ptrckfrnk/sleep-position-classification/Sleep_position_classifier_PSoC.cydsn/I2C_Interface.h

/* ===============================================
 *
 * Alfonzo Massimo, Canavate Chloé, Franke Patrick
 * Project 05 - Sleep Position Classifier
 * Electronic Technologies and Biosensor Laboratory
 * Academic year 2021 - 2022
 * I2C_Interface.h file
 * \brief Hardware specific I2C interface
 *
 * =============================================== */


#ifndef __I2C_Interface_H
    #define __I2C_Interface_H
    
    #include "cytypes.h"
    #include "ErrorCodes.h"
    
    /** \brief Start the I2C peripheral.
    *   
    *   This function starts the I2C peripheral so that it is ready to work.
    */
    ErrorCode I2C_Peripheral_Start(void);
    
    /** \brief Stop the I2C peripheral.
    *   
    *   This function stops the I2C peripheral from working.
    */
    ErrorCode I2C_Peripheral_Stop(void);
    
    /**
    *   \brief Read one byte over I2C.
    *   
    *   This function performs a complete reading operation over I2C from a single
    *   register.
    *   \param device_address I2C address of the device to talk to.
    *   \param register_address Address of the register to be read.
    *   \param data Pointer to a variable where the byte will be saved.
    */
    ErrorCode I2C_Peripheral_ReadRegister(uint8_t device_address, 
                                          uint8_t register_address,
                                          uint8_t* data);
    
    /** 
    *   \brief Read multiple bytes over I2C.
    *   
    *   This function performs a complete reading operation over I2C from multiple
    *   registers.
    *   \param device_address I2C address of the device to talk to.
    *   \param register_address Address of the first register to be read.
    *   \param register_count Number of registers we want to read.
    *   \param data Pointer to an array where data will be saved.
    */
    ErrorCode I2C_Peripheral_ReadRegisterMulti(uint8_t device_address,
                                               uint8_t register_address,
                                               uint8_t register_count,
                                               uint8_t* data);
    /** 
    *   \brief Write a byte over I2C.
    *   
    *   This function performs a complete writing operation over I2C to a single 
    *   register.
    *   \param device_address I2C address of the device to talk to.
    *   \param register_address Address of the register to be written.
    *   \param data Data to be written
    */
    ErrorCode I2C_Peripheral_WriteRegister(uint8_t device_address,
                                           uint8_t register_address,
                                           uint8_t data);
    
    /** 
    *   \brief Write multiple bytes over I2C.
    *   
    *   This function performs a complete writing operation over I2C to multiple
    *   registers
    *   \param device_address I2C address of the device to talk to.
    *   \param register_address Address of the first register to be written.
    *   \param register_count Number of registers that need to be written.
    *   \param data Array of data to be written
    */
    ErrorCode I2C_Peripheral_WriteRegisterMulti(uint8_t device_address,
                                                uint8_t register_address,
                                                uint8_t register_count,
                                                uint8_t* data);
    
    /**
    *   \brief Check if device is connected over I2C.
    *
    *   This function checks if a device is connected over the I2C lines.
    *   \param device_address I2C address of the device to be checked.
    *   \retval Returns true (>0) if device is connected.
    */
    uint8_t I2C_Peripheral_IsDeviceConnected(uint8_t device_address);
    
#endif // I2C_Interface_H
/* [] END OF FILE */
