ptrckfrnk/sleep-position-classification/Sleep_position_classifier_PSoC.cydsn/ErrorCodes.h

/* ===============================================
 *
 * Alfonzo Massimo, Canavate Chloé, Franke Patrick
 * Project 05 - Sleep Position Classifier
 * Electronic Technologies and Biosensor Laboratory
 * Academic year 2021 - 2022
 * ErrorCodes.h file
 * \brief Error codes definition
 *
 * =============================================== */


/**
*   \brief Error codes.
* 
*   This definition defines several error codes that will
*   be used throughout the project.
*/
#ifndef __ERRORCODES_H
    #define __ERRORCODES_H
    
    typedef enum {
        NO_ERROR,           ///< No error generated
        ERROR               ///< Error generated
    } ErrorCode;

#endif
/* [] END OF FILE */
