ptrckfrnk/sleep-position-classification/Sleep_position_classifier_PSoC.cydsn/cyapicallbacks.h

/* ===============================================
 *
 * Alfonzo Massimo, Canavate Chloé, Franke Patrick
 * Project 05 - Sleep Position Classifier
 * Electronic Technologies and Biosensor Laboratory
 * Academic year 2021 - 2022
 * cyapicallbacks.h file
 *
 * =============================================== */


#ifndef CYAPICALLBACKS_H
#define CYAPICALLBACKS_H
    

    /*Define your macro callbacks here */
    /*For more information, refer to the Writing Code topic in the PSoC Creator Help.*/

    
#endif /* CYAPICALLBACKS_H */   
/* [] */
